leonardoward/eja-onboard-gateway-electronics/img/Onboard Gateway V1.0 03.png

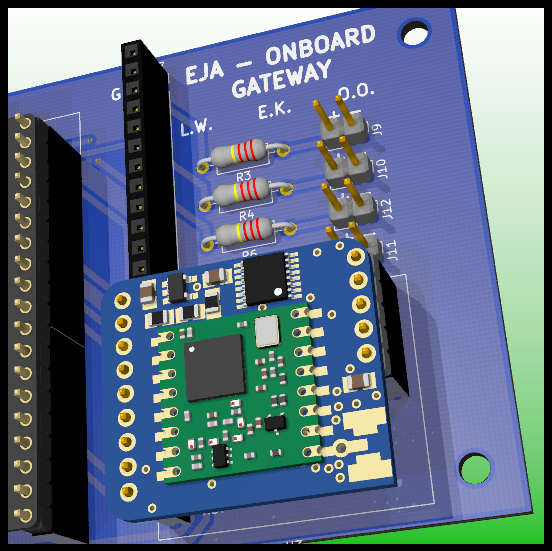
img/Onboard Gateway V1.0 03.png
