leonardoward/eja-onboard-gateway-electronics/img/Onboard Gateway V1.0 07.png

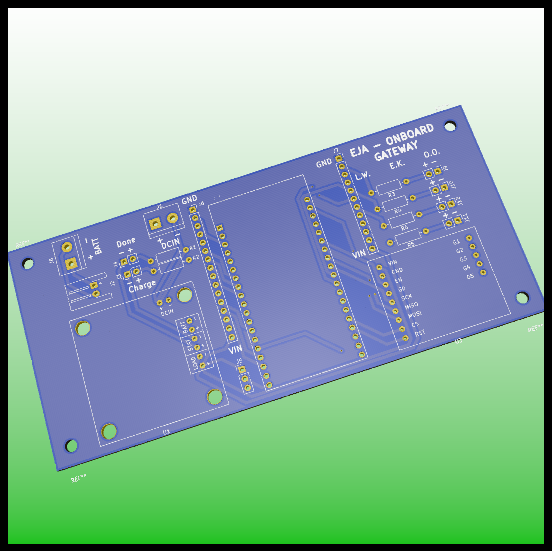
img/Onboard Gateway V1.0 07.png
