leonardoward/eja-onboard-gateway-electronics/img/Onboard_Gateway_01.jpg

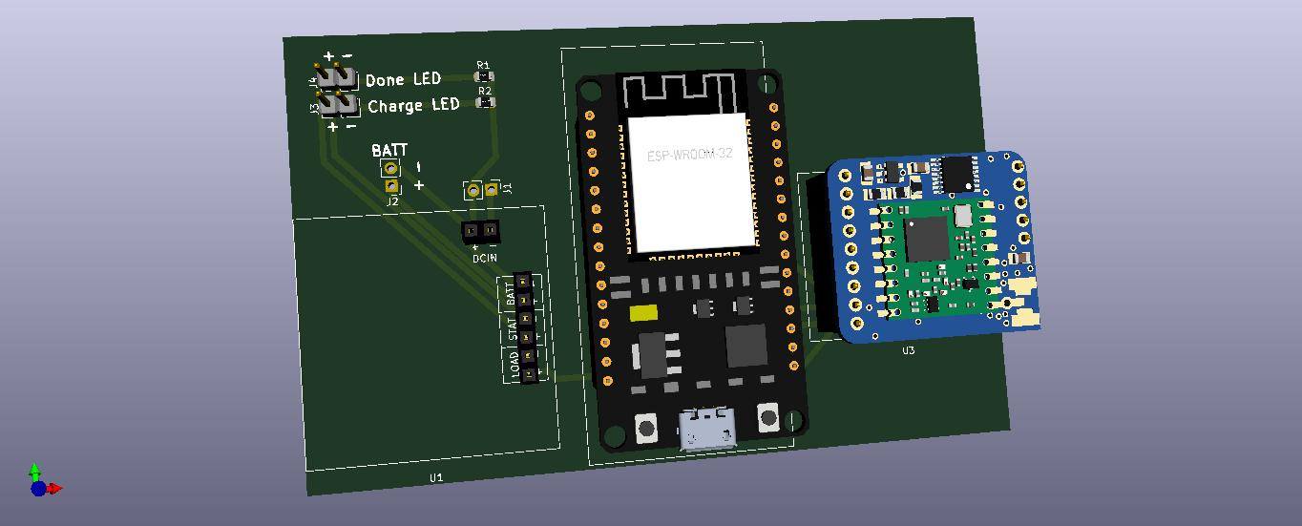
img/Onboard_Gateway_01.jpg
