leonardoward/eja-onboard-gateway-electronics/projects_statLED.gif

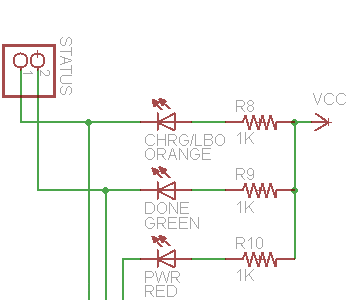
projects_statLED.gif
