leonardoward/eja-onboard-gateway-electronics/3D/Pin Header 1x12 TH Pitch 2.54mm.stp

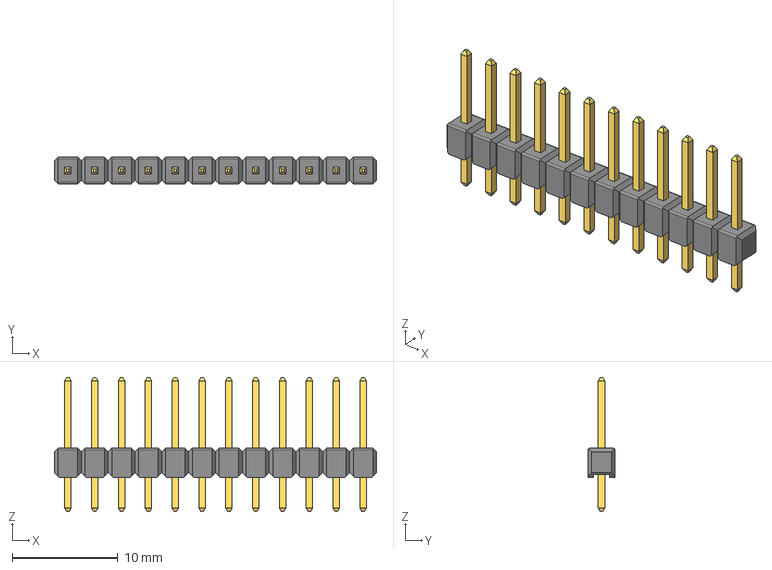
[picture p33: CAD file, 2020-09-28]
3D/Pin Header 1x12 TH Pitch 2.54mm.stp
30.5 x 2.54 x 12.7 mm
