leonardoward/eja-onboard-gateway-electronics/3D/Pin Header 1x5 TH Pitch 2.54mm.stp

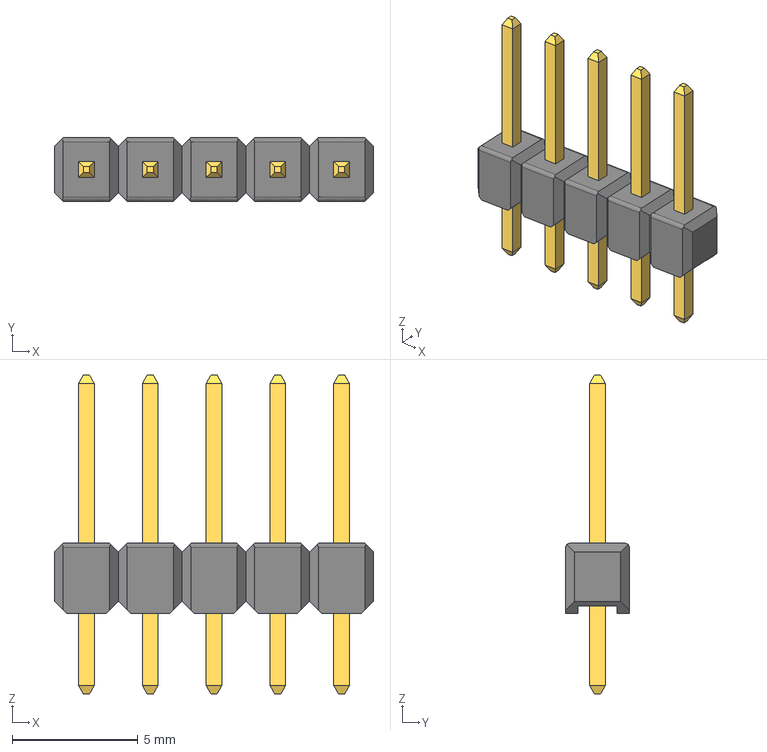
[picture p34: CAD file, 2020-09-28]
3D/Pin Header 1x5 TH Pitch 2.54mm.stp
12.7 x 2.54 x 12.7 mm
